StoneLabs/AVR-Programmer/firmware-programmer/src/programmer/bbprogrammer.h

#pragma once

#if defined(ARDUINO) && ARDUINO >= 100
	#include "arduino.h"
#else
	#include "WProgram.h"
#endif

#include "../softwarespi/SoftwareSPI.h"
#include "../debug.h"
#include "signatues.h"

#define NUMITEMS(arg) ((unsigned int) (sizeof (arg) / sizeof (arg [0])))
#define UNKNOWN_SIGNATURE 255

// DISABLING CAN PERMANENTLY DISABLE THE TARGET CHIP!
#define SAFETY_CHECKS true

#if !SAFETY_CHECKS
#pragma message("SAFETY_CHECK: Disabled!")
#endif

namespace programmer
{


    class BBProgrammer 
    {
    private:
        // programming commands to send via SPI to the chip
        enum {
            programEnable = 0xAC,

            /* writes are preceded by programEnable */
            /**/ chipErase = 0x80,
            /**/ writeLockByte = 0xE0,
            /**/ writeLowFuseByte = 0xA0,
            /**/ writeHighFuseByte = 0xA8,
            /**/ writeExtendedFuseByte = 0xA4,

            pollReady = 0xF0,

            programAcknowledge = 0x53,

            readSignatureByte = 0x30,
            readCalibrationByte = 0x38,

            readLowFuseByte = 0x50, readLowFuseByteArg2 = 0x00,
            readExtendedFuseByte = 0x50, readExtendedFuseByteArg2 = 0x08,
            readHighFuseByte = 0x58, readHighFuseByteArg2 = 0x08,
            readLockByte = 0x58, readLockByteArg2 = 0x00,

            readProgramMemory = 0x20,
            writeProgramMemoryPage = 0x4C,
            loadExtendedAddressByte = 0x4D,

            loadProgramMemoryPageLow = 0x40,
            loadProgramMemoryPageHigh = 0x48,
        };

    public:
        typedef struct {
            byte low;
            byte high;
            byte extended;
            byte lock;
            byte calibration;

            // Get fuse by signature.h fuse enum
            byte get(byte fuse) const;
        } Fuse;

    private:
        bool isProgramming = false;
        SoftwareSPI* spi;
        Signature* signature = nullptr;
        Fuse fuses;

    private:
        byte execCommand(const byte b1, const byte b2 = 0, const byte b3 = 0, const byte b4 = 0);
        void pollUntilReady();

    public:
        BBProgrammer(const byte p_sck, const byte p_mosi, const byte p_miso, const byte p_reset);
        ~BBProgrammer();

        bool startProgramming(const unsigned int tries);
        void stopProgramming();

        void readSignatureBytes(byte& b1, byte& b2, byte& b3);
        bool readSignature();
        const Signature* getSignature() const;

        void readFuses();
        const Fuse& getFuses() const;

        bool setHighFuse(const byte fuse);
        void setLowFuse(const byte fuse);
		void setExtFuse(const byte fuse);
		void setLockBits(const byte fuse);

        void flashPage(unsigned long pageaddr, byte* pagebuffer);
        void erase();
    };
}
