StoneLabs/AVR-Programmer/firmware-uim/src/tabPage.cpp

#include "tabPage.h"

byte TabPage::getTabIndex() const
{
    return this->tabIndex;
}

TabPage::TabPage(PageManager* manager, byte tabLength)
    : Page ( manager ), tabLength (tabLength)
{
}

void TabPage::left()
{
    if (this->tabIndex == 0)
        this->tabIndex = this->tabLength-1;
    else
        this->tabIndex--;
    this->tabIndex %= this->tabLength;
}

void TabPage::right()
{
    this->tabIndex++;
    this->tabIndex %= this->tabLength;
}
